foobarflies/pianette/_Resources/Hardware/PCB Files/PDF/BusBoard/BusBoard_etch_silk_bottom.pdf

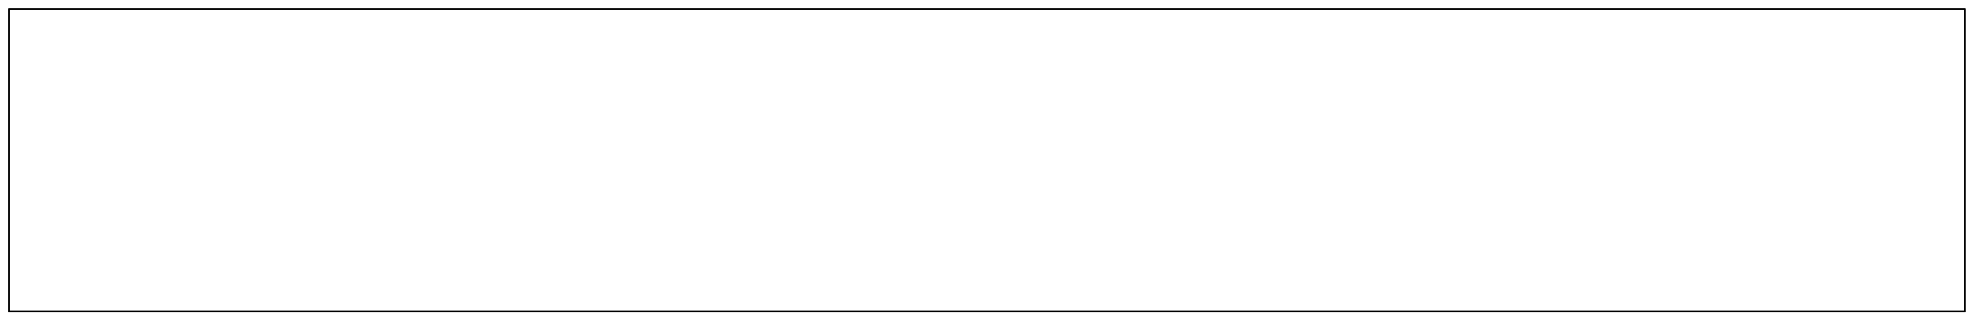
[picture p5: page 1]
