foobarflies/pianette/_Resources/Hardware/PCB Files/PDF/BusBoard/BusBoard_etch_silk_bottom_mirror.pdf

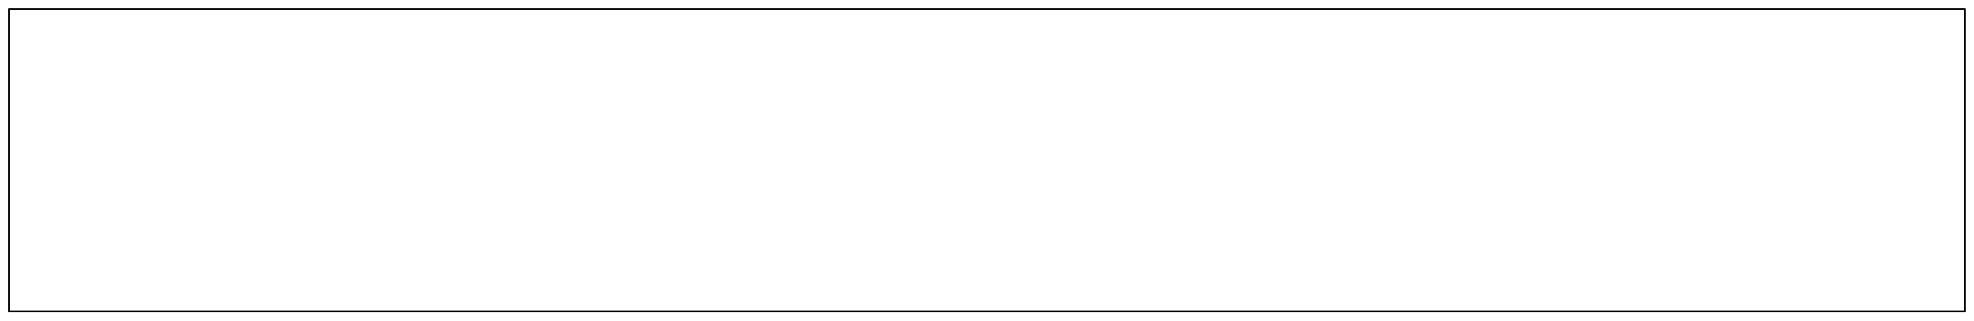
[picture p6: page 1]
