foobarflies/pianette/_Resources/Hardware/PCB Files/PDF/BusBoard/BusBoard_etch_silk_top.pdf

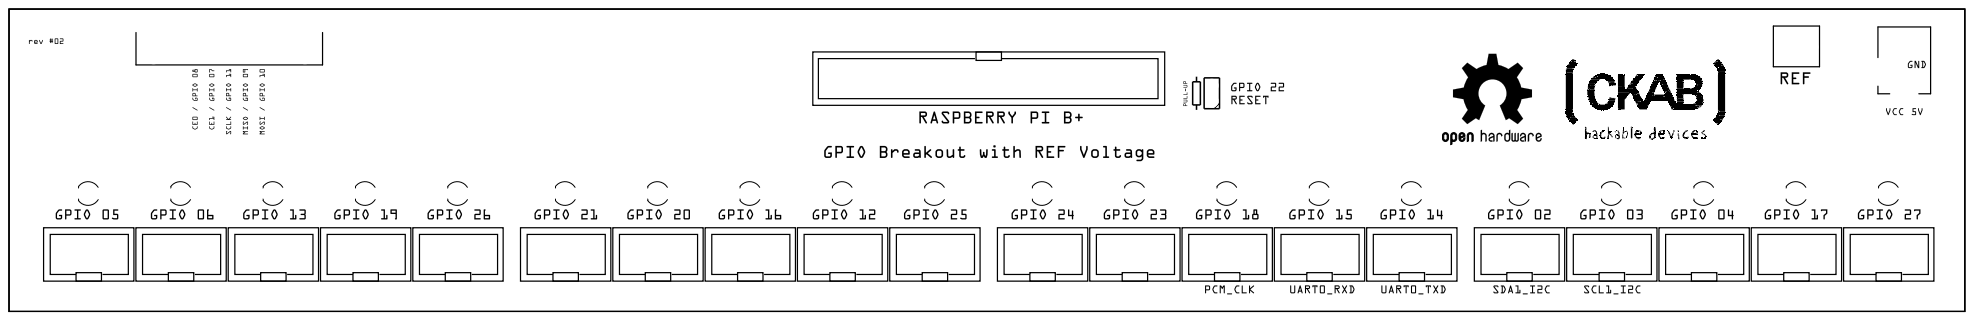
[picture p21: page 1]
