foobarflies/pianette/_Resources/Hardware/PCB Files/PDF/BusBoard/BusBoard_etch_silk_top_mirror.pdf

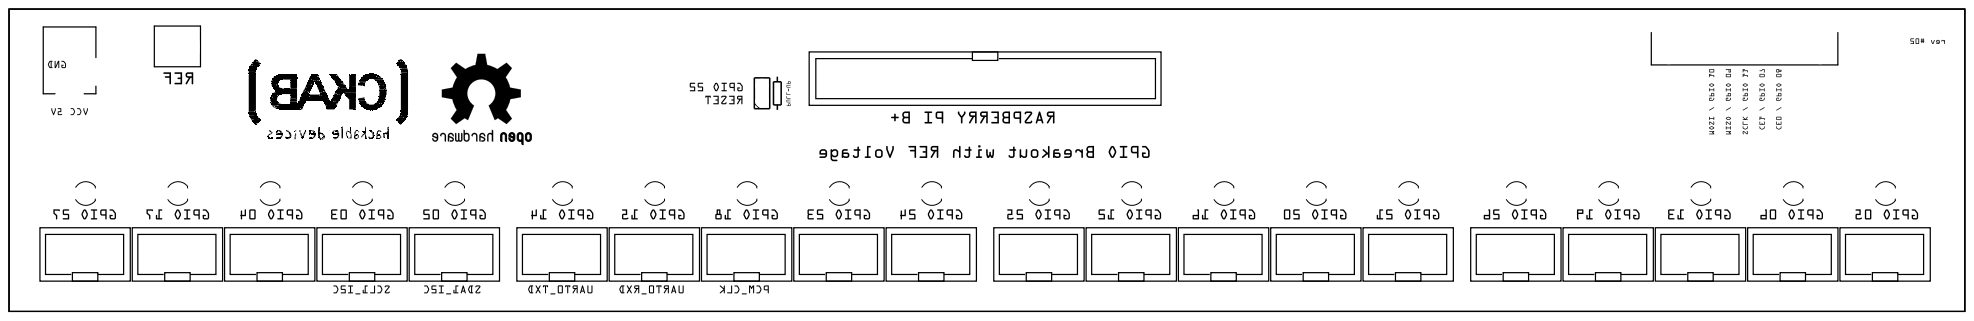
[picture p22: page 1]
