foobarflies/pianette/_Resources/Hardware/PCB Files/PDF/AnalogTrigger/AnalogTrigger_etch_copper_bottom.pdf

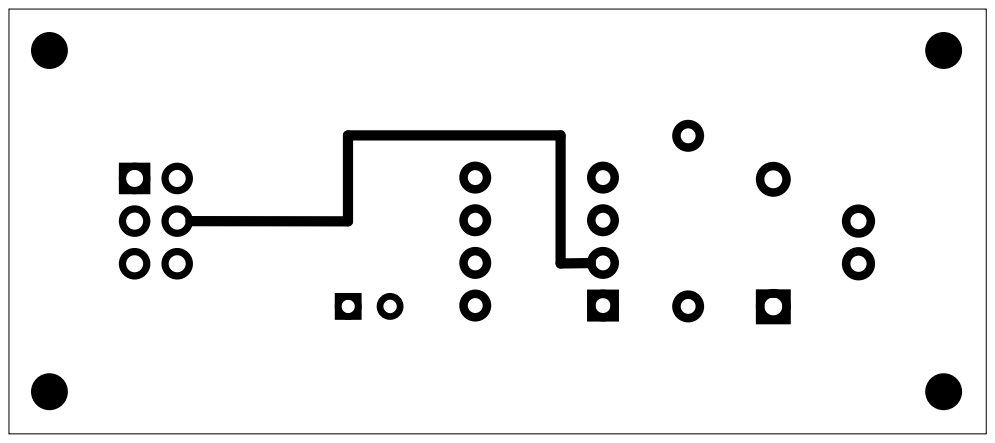
[picture p23: page 1]
