foobarflies/pianette/_Resources/Hardware/PCB Files/PDF/AnalogTrigger/AnalogTrigger_etch_copper_bottom_mirror.pdf

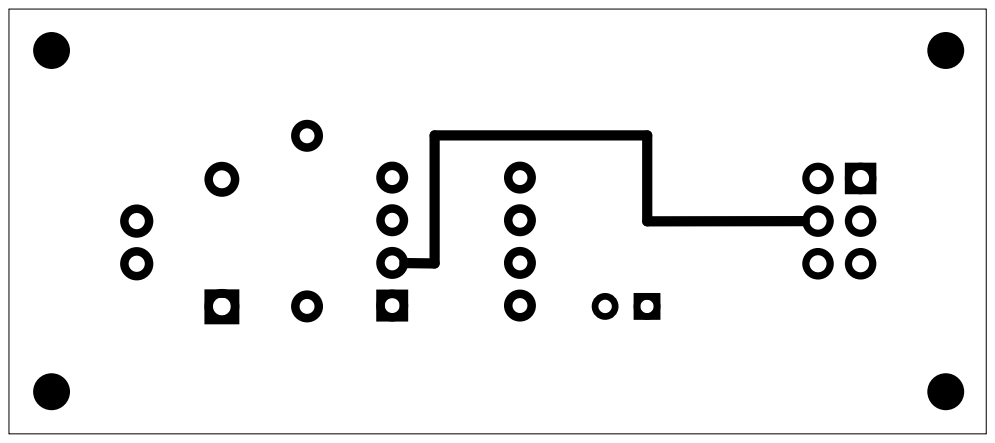
[picture p24: page 1]
