foobarflies/pianette/_Resources/Hardware/PCB Files/PDF/AnalogTrigger/AnalogTrigger_etch_copper_top.pdf

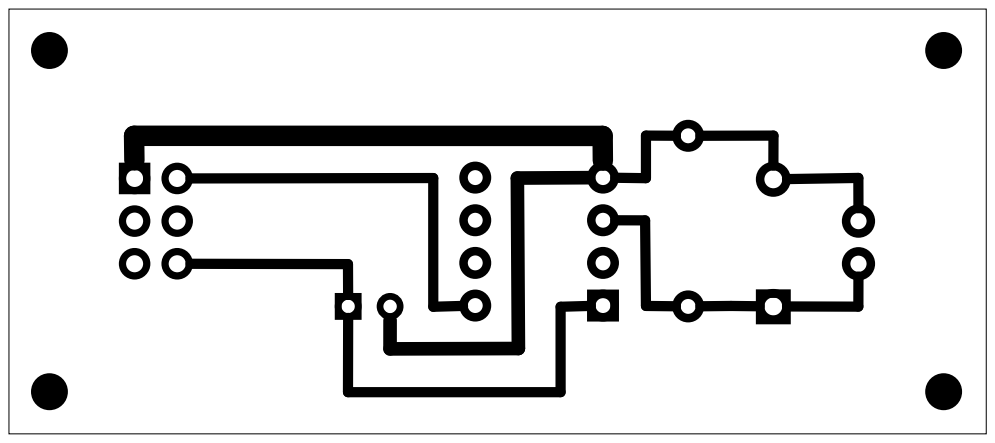
[picture p25: page 1]
