foobarflies/pianette/_Resources/Hardware/PCB Files/PDF/AnalogTrigger/AnalogTrigger_etch_copper_top_mirror.pdf

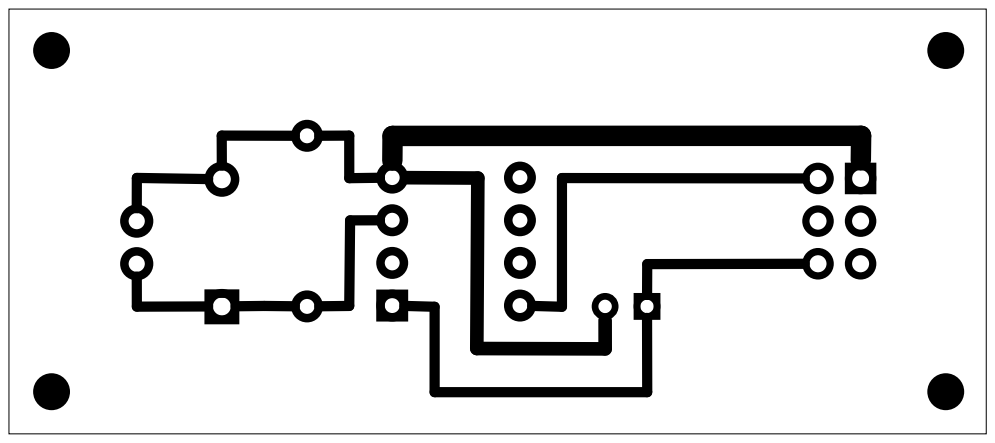
[picture p26: page 1]
