foobarflies/pianette/_Resources/Hardware/PCB Files/PDF/AnalogTrigger/AnalogTrigger_etch_mask_bottom.pdf

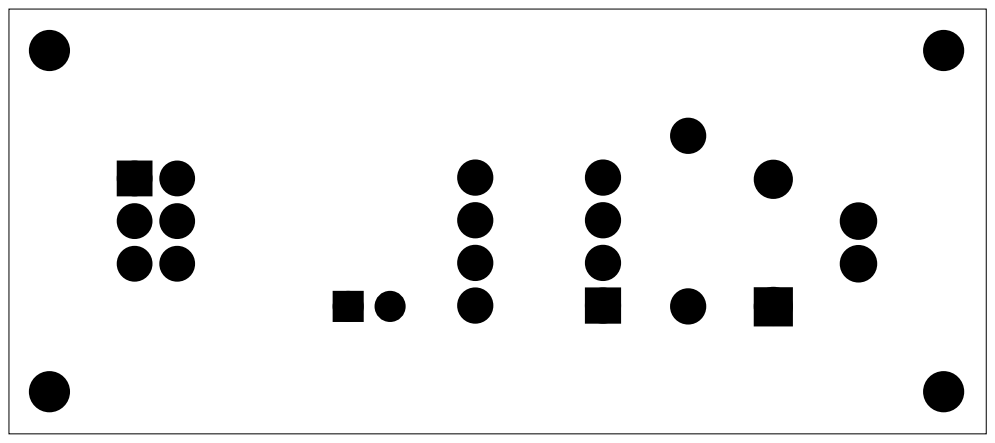
[picture p27: page 1]
