foobarflies/pianette/_Resources/Hardware/PCB Files/PDF/AnalogTrigger/AnalogTrigger_etch_mask_bottom_mirror.pdf

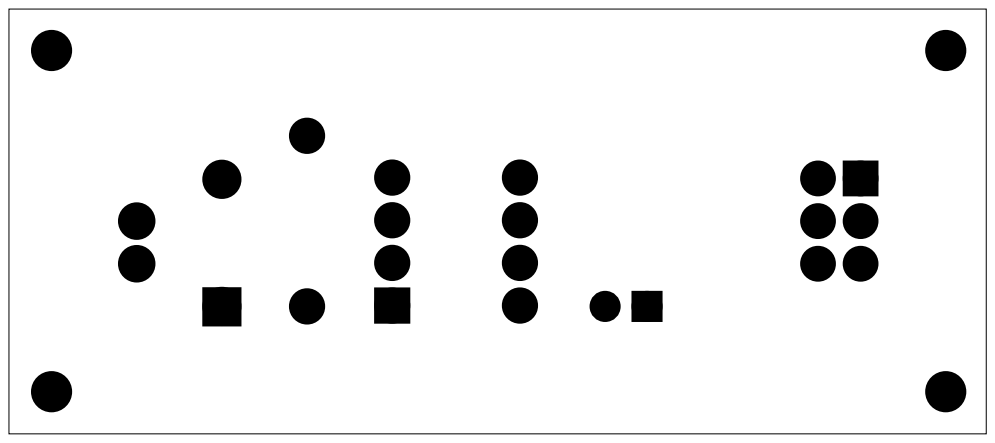
[picture p28: page 1]
