foobarflies/pianette/_Resources/Hardware/PCB Files/PDF/AnalogTrigger/AnalogTrigger_etch_silk_bottom.pdf

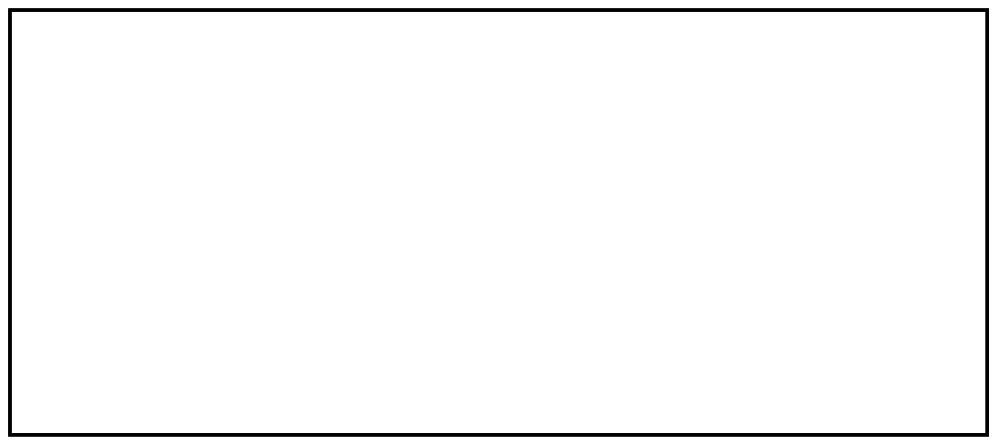
[picture p29: page 1]
