foobarflies/pianette/_Resources/Hardware/PCB Files/PDF/AnalogTrigger/AnalogTrigger_etch_silk_top_mirror.pdf

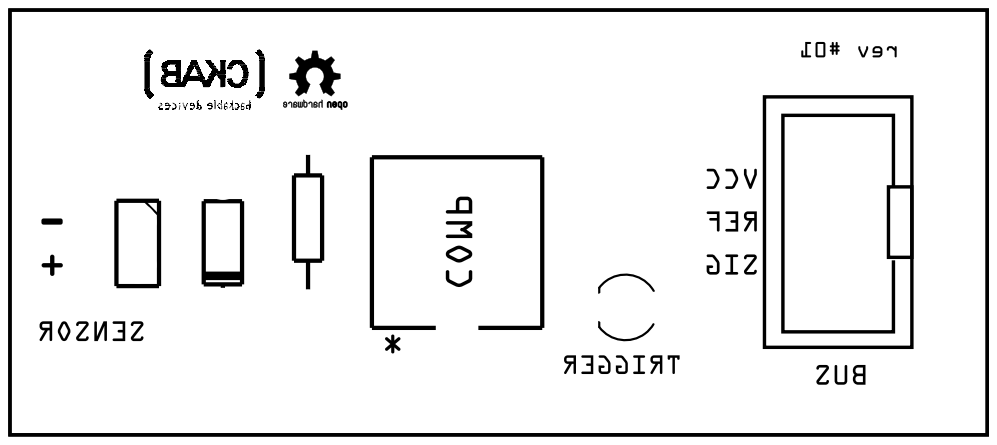
[picture p31: page 1]
