foobarflies/pianette/_Resources/Hardware/PCB Files/PDF/ArduinoBoard/ArduinoBoard_etch_copper_bottom.pdf

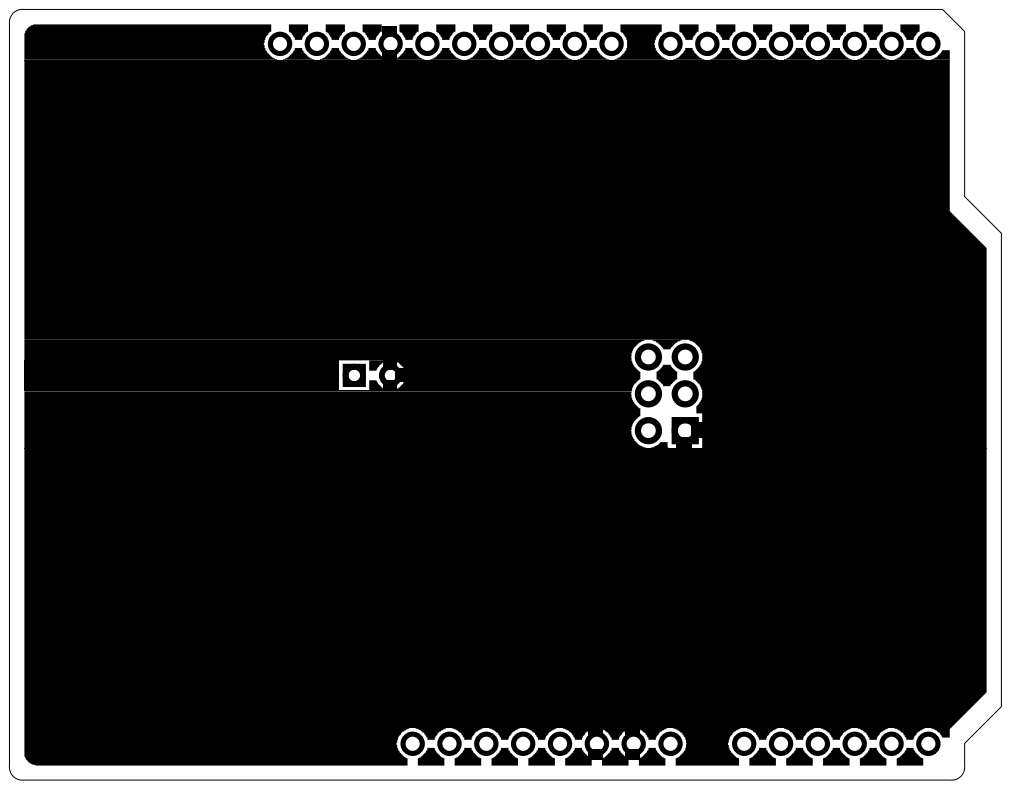
[picture p32: page 1]
