foobarflies/pianette/_Resources/Hardware/PCB Files/PDF/ArduinoBoard/ArduinoBoard_etch_copper_bottom_mirror.pdf

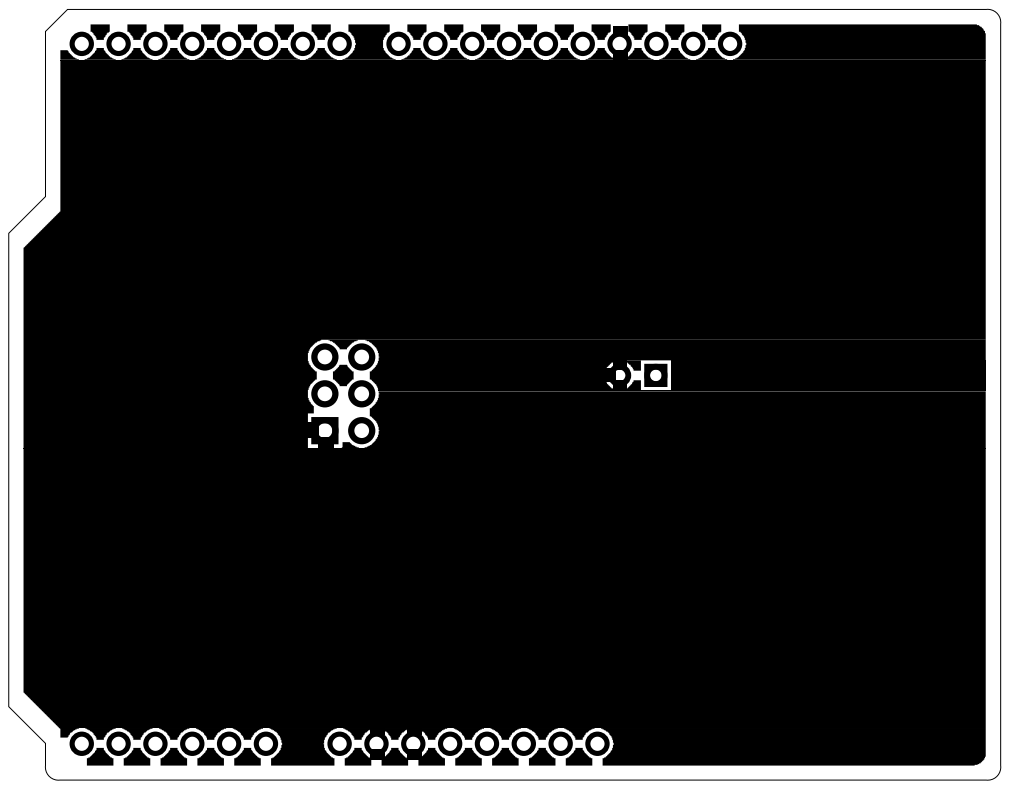
[picture p33: page 1]
