foobarflies/pianette/_Resources/Hardware/PCB Files/PDF/ArduinoBoard/ArduinoBoard_etch_copper_top.pdf

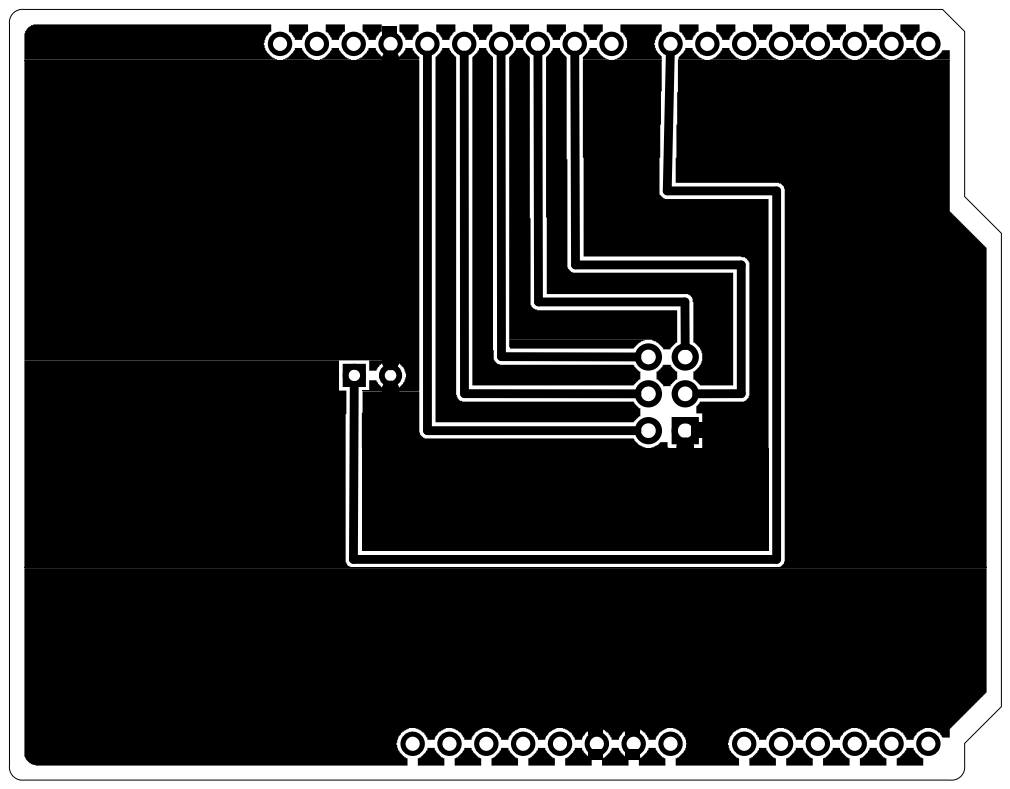
[picture p34: page 1]
