foobarflies/pianette/_Resources/Hardware/PCB Files/PDF/ArduinoBoard/ArduinoBoard_etch_copper_top_mirror.pdf

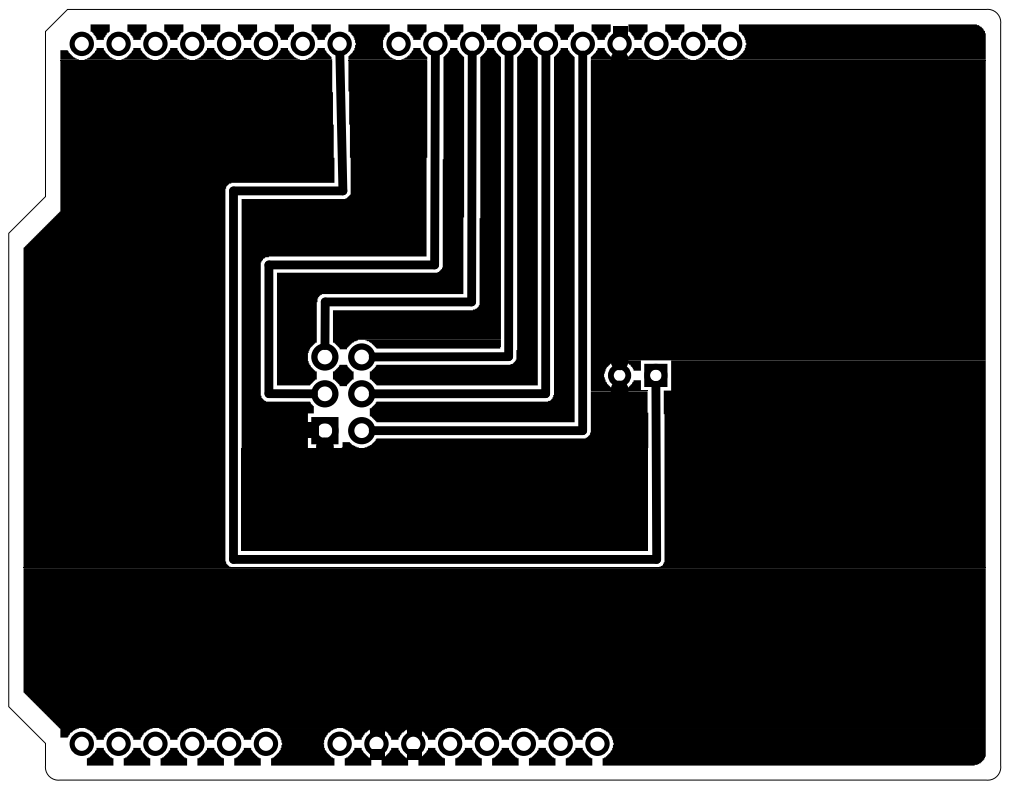
[picture p35: page 1]
