foobarflies/pianette/_Resources/Hardware/PCB Files/PDF/ArduinoBoard/ArduinoBoard_etch_mask_bottom.pdf

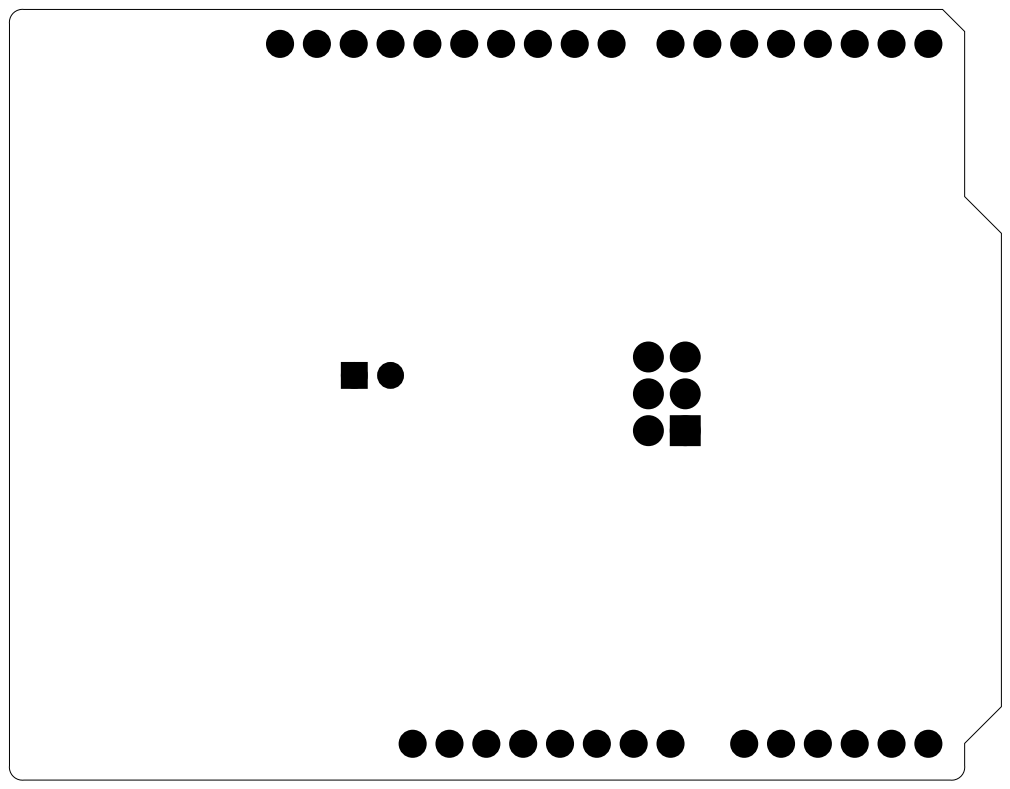
[picture p36: page 1]
