foobarflies/pianette/_Resources/Hardware/PCB Files/PDF/ArduinoBoard/ArduinoBoard_etch_mask_bottom_mirror.pdf

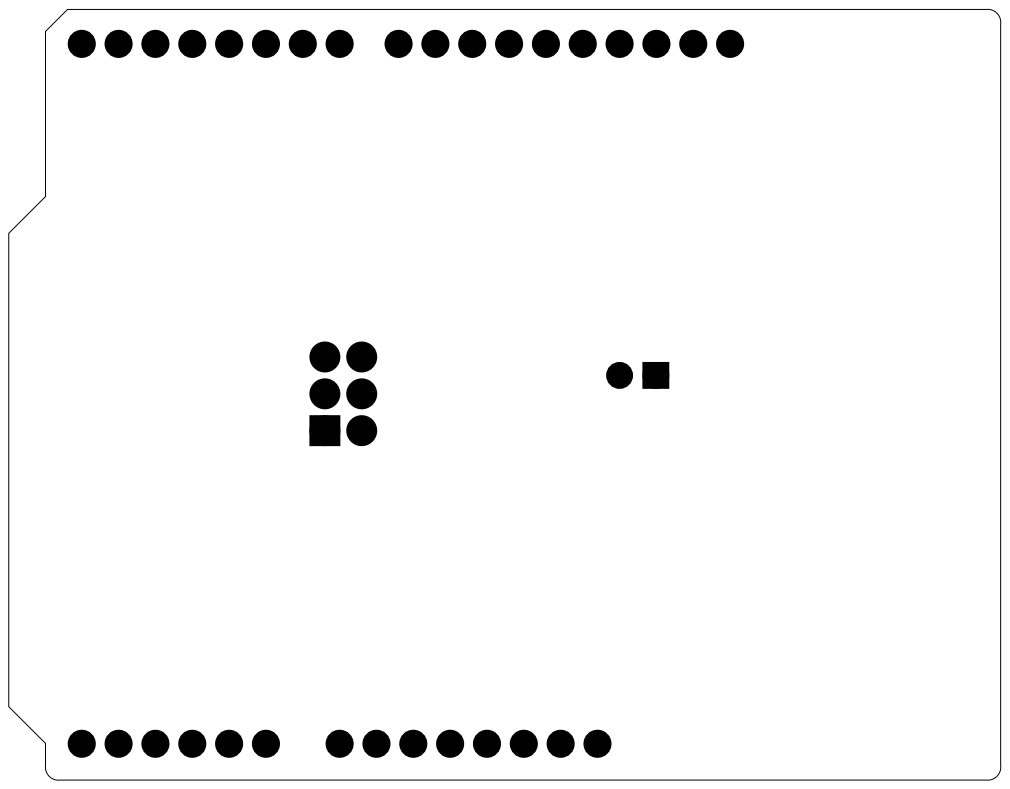
[picture p37: page 1]
