foobarflies/pianette/_Resources/Hardware/PCB Files/PDF/ArduinoBoard/ArduinoBoard_etch_silk_bottom.pdf

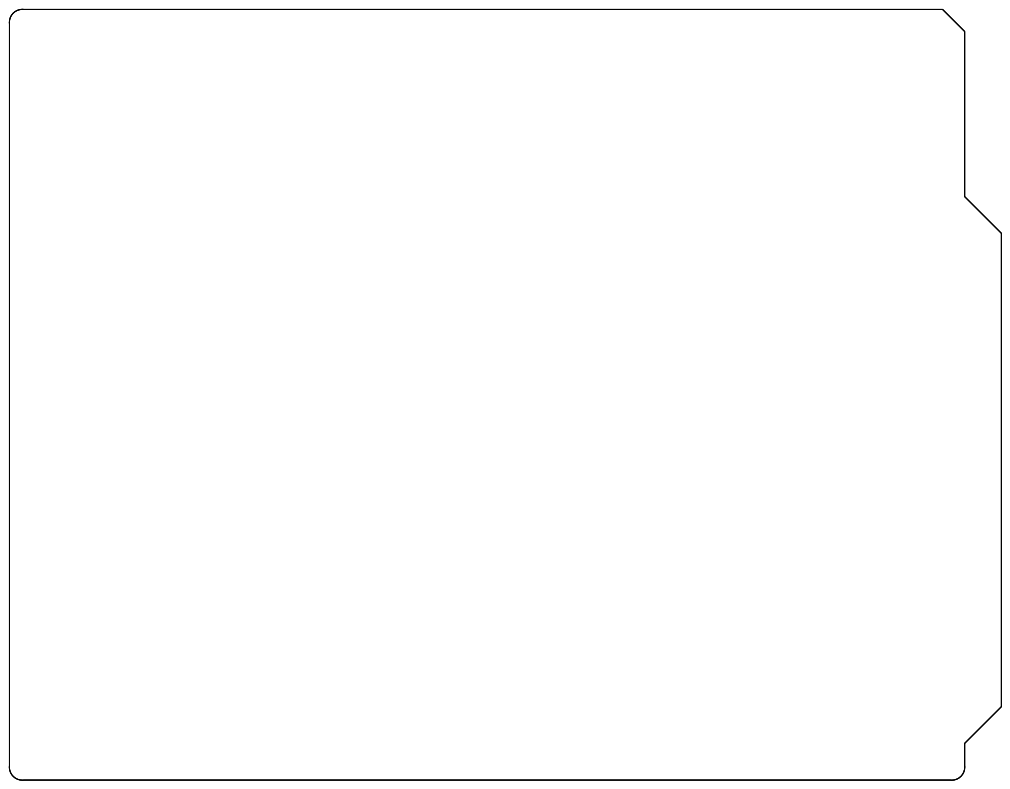
[picture p38: page 1]
