foobarflies/pianette/_Resources/Hardware/PCB Files/PDF/ArduinoBoard/ArduinoBoard_etch_silk_bottom_mirror.pdf

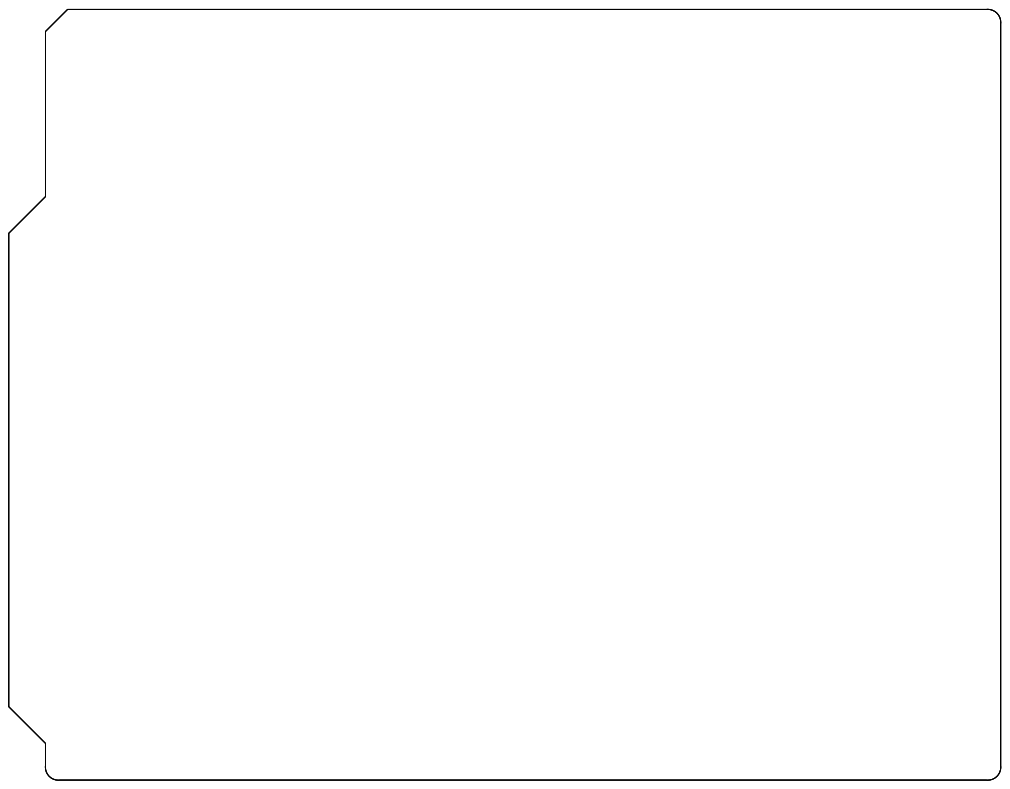
[picture p39: page 1]
