foobarflies/pianette/_Resources/Hardware/PCB Files/PDF/ArduinoBoard/ArduinoBoard_etch_silk_top_mirror.pdf

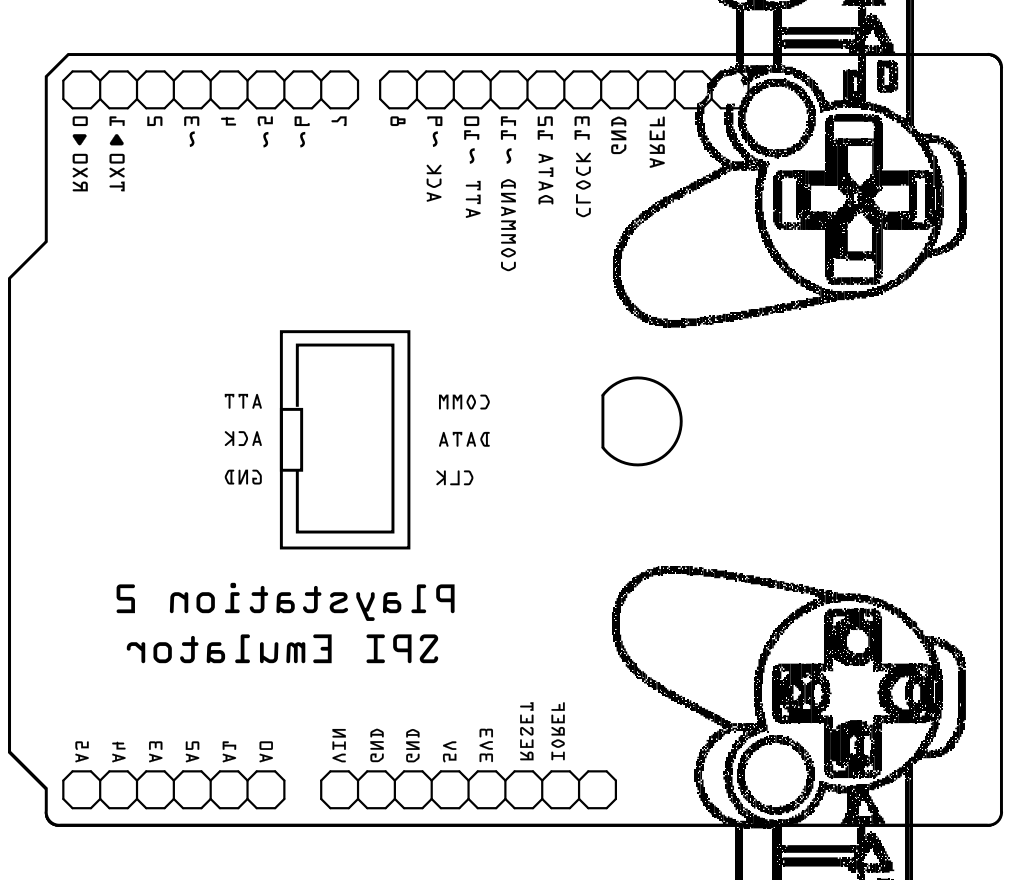
[picture p41: page 1]
