foobarflies/pianette/models/GPIOController.py

# coding=utf-8

from utils import *
import warnings

import RPi.GPIO as GPIO

GPIO.setmode(GPIO.BCM)

# We want to be able to catch warnings, expecially the RuntimeWarning when a pin is already attached
warnings.filterwarnings('error')

# Just to be sure ...
# THIS LINE WILL ISSUE A WARNING THAT CAN HOPEFULLY BE IGNORED
GPIO.cleanup()

"""
# Global GPIO Pin Mapping
"""
GPIO_PIN_ATTACHMENTS = {
    # Bank 1
    5: { "note": "C3" },
    6: { "note": "D3" },
    13: { "note": "E3" },
    19: { "note": "F3" },
    26: { "note": "G3" },

    # Bank 2
    21: { "note": "A4" },
    20: { "note": "B♭4" },
    16: { "note": "B4" },
    12: { "note": "C4" },
    25: None,
    22: { "pull_up_down": GPIO.PUD_UP, "event": GPIO.FALLING, "command": "RESET" },

    # Bank 3
    24: { "note": "C5" },
    23: { "note": "D5" },
    18: { "note": "E♭5" },
    15: { "note": "E5" },
    14: { "note": "F5" },

    # Bank 4
    2: { "note": "G♭5" },
    3: { "note": "G5" },
    4: { "note": "A6" },
    17: { "note": "B♭6" },
    27: { "note": "B6" },
}

class GPIOController:
    def __init__(self, piano_state, controller_state):
        self.piano_state = piano_state
        self.controller_state = controller_state

        # Attach callbacks to pins
        Debug.println("INFO", "Attaching event callbacks to pins ...")

        for pin, attachment in GPIO_PIN_ATTACHMENTS.items():
            if attachment:
                pull_up_down = attachment.get("pull_up_down", GPIO.PUD_DOWN)
                event = attachment.get("event", GPIO.RISING)

                callback = None
                callback_description = None

                if "note" in attachment:
                    callback = self.gpio_pin_note_callback
                    callback_description = "Note %s" % attachment["note"]
                elif "command" in attachment:
                    callback = self.gpio_pin_command_callback
                    callback_description = "Command %s" % attachment["command"]
                if callback is None:
                    Debug.println("FAIL", "Could not attach event callback for pin %2d" % (pin))
                    raise Exception()

                try:
                    GPIO.setup(pin, GPIO.IN, pull_up_down = pull_up_down)
                    GPIO.add_event_detect(pin, event, callback=callback, bouncetime=300)
                except Exception:
                    if (pin in {14, 15, 18}): # UART Pins, we can override
                        Debug.println("WARNING", "UART Pin %2d already in use. Overriding ..." % (pin))
                    else: # Nope nope nope nope, nope.
                        Debug.println("FAIL", "Pin %2d already in use." % (pin))
                        raise
                Debug.println("SUCCESS", "Pin %2d attached to %s" % (pin, callback_description) )
            else:
                Debug.println("WARNING", "Pin %2d not attached" % (pin) )

    def __del__(self):
        # Cleanup GPIOs on object destruction
        GPIO.cleanup()

    # Callback method for PSX Controller Commands
    def gpio_pin_command_callback(self, channel):
        command = GPIO_PIN_ATTACHMENTS[channel]["command"]
        Debug.println("INFO", "Pin %2d activated : triggering PSX Controller Command %s" % (channel, command) )
        self.controller_state.raiseFlag("RESET")

    # Callback method for Piano Notes
    def gpio_pin_note_callback(self,channel):
        note = GPIO_PIN_ATTACHMENTS[channel]["note"]
        Debug.println("INFO", "Pin %2d activated : triggering Piano Note %s" % (channel, note) )
        self.piano_state.raise_note(note)
