foobarflies/pianette/models/Pianette.py

# coding=utf-8

from copy import deepcopy
from utils import *
from models import ConsoleController

import threading

# Pianette Configuration

# Period of I/O cycle, in seconds
PIANETTE_CYCLE_PERIOD = 10/1000 # Seems to properly operate between 7 msecs and 26 msecs (PSX observation)

# Number of cycles before Inputs are processed and sent to Output
PIANETTE_PROCESSING_CYCLES = 2

# Mapping: Piano Notes (input) => PSX Controller Combo (output)
PIANETTE_BUFFERED_STATES_MAPPINGS = [
    # Single Notes (left hand): Moves
    {
        "piano": [ "C3" ],
        "psx_controller": { "LEFT": [ 10 ] },
    },
    {
        "piano": [ "D3" ],
        "psx_controller": { "LEFT": [ 5 ] },
    },
    {
        "piano": [ "F3" ],
        "psx_controller": { "DOWN": [ 10 ] },
    },
    {
        "piano": [ "A4" ],
        "psx_controller": { "RIGHT": [ 5 ] },
    },
    {
        "piano": [ "B4" ],
        "psx_controller": { "RIGHT": [ 10 ] },
    },

    # Single Notes (right hand): Simple Strikes
    {
        "piano": [ "C5" ],
        "psx_controller": { "S": [ 3 ] },
    },
    {
        "piano": [ "D5" ],
        "psx_controller": { "O": [ 3 ] },
    },
    {
        "piano": [ "E5" ],
        "psx_controller": { "X": [ 3 ] },
    },
    {
        "piano": [ "F5" ],
        "psx_controller": { "S": [ 3 ] },
    },
    {
        "piano": [ "G5" ],
        "psx_controller": { "O": [ 3 ] },
    },
    {
        "piano": [ "A6" ],
        "psx_controller": { "T": [ 3 ] },
    },
    {
        "piano": [ "B6" ],
        "psx_controller": { "T": [ 3 ] },
    },

    # Chords (left hand): Combo Moves!
    {
        # LEFT1 + CL1 + CL2 (Do majeur) => UP
        "piano": [ "C3", "E3", "G3" ],
        "psx_controller": { "UP" : [ 3 ] },
    },
    {
        # LEFT1 + CL4 (Do octave) => UP
        "piano": [ "C3", "C4" ],
        "psx_controller": { "UP" : [ 3 ] },
    },
    {
        # LEFT1 + CL1 + CL2 + CL3 (Do majeur 7e) => UP + Kick droit (ou gauche suivant player)
        "piano": [ "C3", "E3", "G3", "B♭4" ],
        "psx_controller": { "UP" : [ 3 ], "X": [ -1, 3 ] },
    },
    {
        # CL1 + CL2 + CL4 (Do Majeur premier renversement) => UP+RIGHT
        "piano": [ "E3", "G3", "C4" ],
        "psx_controller": { "RIGHT" : [ 3 ], "UP": [ -1, 3 ] },
    },
    {
        # LEFT1 + DOWN (Do Dim 4) => DOWN+LEFT
        "piano": [ "C3", "F3" ],
        "psx_controller": { "DOWN" : [ 3 ], "LEFT": [ 3 ] },
    },
    {
        # LEFT2 + DOWN (Ré Min) => DOWN+LEFT
        "piano": [ "D3", "F3" ],
        "psx_controller": { "DOWN" : [ 3 ], "LEFT": [ 3 ] },
    },
    {
        # RIGHT1 + DOWN (Ré min) => RIGHT+DOWN
        "piano": [ "A4", "F3" ],
        "psx_controller": { "DOWN" : [ 3 ], "RIGHT": [ 3 ] },
    },
    {
        # RIGHT2 + DOWN (Si) => RIGHT+DOWN
        "piano": [ "B4", "F3" ],
        "psx_controller": { "DOWN" : [ 3 ], "RIGHT": [ 3 ] },
    },

    # Chords (right hand): Combo Strikes!

    {
        # S1 + X1 + O1 (Do majeur) => Tatsukami
        "piano": [ "C5", "E5", "D5" ],
        "psx_controller": { "DOWN" : [ 1, 3 ],  "RIGHT" : [ -1, 3, 3 ], "X" : [ -1, -3, -3, 10] },
    },
    {
        # S1 + X1 + O1 + CR3 (Do 7e) => Hadouken
        "piano": [ "C5", "E5", "D5", "B♭6" ],
        "psx_controller": { "DOWN" : [ 1, 3 ],  "LEFT" : [ -1, 3, 3 ], "S" : [ -1, -3, -3, 10] },
    },
    {
        # S1 + S2 + T1 (Do 6) => ?
        "piano": [ "C5", "F5", "A6" ],
        "psx_controller": {},
    },
    {
        # S1 + CR1 + O1 (Do min) => ?
        "piano": [ "C5", "E♭5", "D5" ],
        "psx_controller": {},
    },
    {
        # S1 + CR1 + O1 + CR3 (Do min 7e) => ?
        "piano": [ "C5", "E♭5", "D5", "B♭6" ],
        "psx_controller": {},
    },
    {
        # S1 + CR1 + CR2 + CR3 (Dim 3) => ?
        "piano": [ "C5", "E5", "G♭5", "B♭6" ],
        "psx_controller": {},
    },

    # "Combo Enabler" keys, no direct mapping
    # "E3" (AKA "CL1")
    # "G3" (AKA "CL2")
    # "B♭4" (AKA "CL3")
    # "C4" (AKA "CL4")
    # "E♭5" (AKA "CR1")
    # "G♭5" (AKA "CR2")
    # "B♭6" (AKA "CR3")
]

# Assign a unique, combinable bitid to configured notes
_NOTE_BITIDS = {}

_current_note_bitid = 0b1
for buffered_state_mapping in PIANETTE_BUFFERED_STATES_MAPPINGS:
    for note in buffered_state_mapping["piano"]:
        if not note in _NOTE_BITIDS:
            _NOTE_BITIDS[note] = _current_note_bitid
            _current_note_bitid <<= 1
del _current_note_bitid

# Structure Buffered States Mapping using Piano "Chords" bitids (combination of Note bitids)
# Rank chords as follows:
#   1- chords with more notes have a higher priority
#   2- for an equal number of notes, chords declared first in config have a higher priority
_ranked_chord_bitids_for_note_count = {}

_BUFFERED_STATES_MAPPING_FOR_CHORD_BITID = {}
for buffered_state_mapping in PIANETTE_BUFFERED_STATES_MAPPINGS:
    chord_bitid = 0b0
    note_count = len(buffered_state_mapping["piano"])

    for note in buffered_state_mapping["piano"]:
        chord_bitid |= _NOTE_BITIDS[note]

    _BUFFERED_STATES_MAPPING_FOR_CHORD_BITID[chord_bitid] = buffered_state_mapping
    chord_bitids = _ranked_chord_bitids_for_note_count.get(note_count, [])
    chord_bitids.append(chord_bitid)
    _ranked_chord_bitids_for_note_count[note_count] = chord_bitids

_RANKED_CHORD_BITIDS = []
for note_count in sorted(list(_ranked_chord_bitids_for_note_count.keys()), reverse = True):
    _RANKED_CHORD_BITIDS.extend(_ranked_chord_bitids_for_note_count[note_count])
del _ranked_chord_bitids_for_note_count

def get_notes_chord_bitid(notes):
    notes_bitids = [ _NOTE_BITIDS[note] for note in notes ]
    notes_chord_bitid = 0b0
    for bitid in notes_bitids:
        notes_chord_bitid |= bitid
    return notes_chord_bitid

def get_ranked_chord_bitids_including_at_least_one_of_notes(notes, from_chord_bitids_pool = _RANKED_CHORD_BITIDS):
    notes_chord_bitid = get_notes_chord_bitid(notes)

    ranked_notes_chord_bitids = []
    for chord_bitid in from_chord_bitids_pool:
        if (chord_bitid & notes_chord_bitid):
            ranked_notes_chord_bitids.append(chord_bitid)

    return ranked_notes_chord_bitids

class Pianette(object):
    def __init__(self, piano_state, psx_controller_state):
        self.piano_state = piano_state
        self.psx_controller_state = psx_controller_state

        # Instantiate the console controller that is responsible for sendint out the psx constroller state to the console
        self.console_controller = ConsoleController(self.psx_controller_state)

        # Upcoming state cycles for the Piano Notes (input)
        self.piano_buffered_states = {
            "C3": [],
            "D3": [],
            "E3": [],
            "F3": [],
            "G3": [],
            "A4": [],
            "B♭4": [],
            "B4": [],
            "C4": [],
            "C5": [],
            "D5": [],
            "E♭5": [],
            "E5": [],
            "F5": [],
            "G♭5": [],
            "G5": [],
            "A6": [],
            "B♭6": [],
            "B6": [],
        }

        # Upcoming state cycles for the PSX Controller (output)
        self.psx_controller_buffered_states = {
            "T" : [],
            "S" : [],
            "X" : [],
            "O" : [],
            "UP" : [],
            "DOWN" : [],
            "LEFT" : [],
            "RIGHT" : [],
            "SELECT" : [],
            "START" : [],
        }

        self._timer = None
        self._timer_interval = PIANETTE_CYCLE_PERIOD
        self._timer_is_running = False

        # Start the timer thread that will cycle buffered states at each interval
        self.start_timer()
        Debug.println("INFO", "Pianette buffered states timer thread started at %f secs interval" % self._timer_interval)

    def __del__(self):
        if hasattr(self, '_timer'):
            self.stop_timer()

    def _run_timer(self):
        self._timer_is_running = False
        self.start_timer()
        self.cycle_buffered_states()

    def start_timer(self):
        if not self._timer_is_running:
            self._timer = threading.Timer(self._timer_interval, self._run_timer)
            self._timer.start()
            self.is_running = True

    def stop_timer(self):
        self._timer.cancel()
        self._timer_is_running = False

    def cycle_buffered_states(self):
        # Input Piano Notes to Piano Buffered States
        for piano_note in self.piano_state.get_notes_keys():
            if self.piano_state.is_note_raised(piano_note):
                Debug.println("INFO", "Processing Piano Note %s" % (piano_note))
                self.piano_buffered_states[piano_note].append({ "cycles_remaining": PIANETTE_PROCESSING_CYCLES })
                self.piano_state.clear_note(piano_note)

        # Process Buffered States: Determine piano note or chord
        # Notes that have reached their last cycle "lead" the chord determination
        # Other notes may be used to "complement" lead notes.
        # If a winning chord is found, push corresponding combo to PSX Controller buffer
        # If complementary notes are actually used, they are discarded from buffer.
        lead_notes = []
        complementary_notes = []
        for piano_note in self.piano_buffered_states.keys():
            processed_buffered_states = []
            for buffered_state in self.piano_buffered_states[piano_note]:
                if buffered_state["cycles_remaining"] == 0:
                    lead_notes.append(piano_note)
                else:
                    complementary_notes.append(piano_note)
                    buffered_state["cycles_remaining"] -= 1
                    processed_buffered_states.append(buffered_state)
            self.piano_buffered_states[piano_note] = processed_buffered_states

        if lead_notes:
            Debug.println("INFO", "Processing Piano Notes: lead=%s, complementary=%s" % (lead_notes, complementary_notes))
            ranked_chord_bitids = get_ranked_chord_bitids_including_at_least_one_of_notes(lead_notes)

            all_notes_chord_bitid = get_notes_chord_bitid(lead_notes + complementary_notes)
            ranked_winning_chord_bitids = [chord_bitid for chord_bitid in ranked_chord_bitids if not ((all_notes_chord_bitid & chord_bitid) ^ chord_bitid)]

            if ranked_winning_chord_bitids:
                winning_chord_bitid = ranked_winning_chord_bitids[0]
                winning_states_mapping = deepcopy(_BUFFERED_STATES_MAPPING_FOR_CHORD_BITID[winning_chord_bitid])

                # Push piano command to PSX Controller buffer, clearing any pending combo
                for control in self.psx_controller_buffered_states.keys():
                    self.psx_controller_buffered_states[control] = winning_states_mapping["psx_controller"].get(control, [])

                # Clear winning chord notes from the piano buffer
                for piano_note in self.piano_buffered_states.keys():
                    if _NOTE_BITIDS[piano_note] & winning_chord_bitid:
                        if self.piano_buffered_states[piano_note]:
                            self.piano_buffered_states[piano_note] = self.piano_buffered_states[piano_note][1:]

        # Output PSX Controller Buffered states to PSX Controller
        for psx_control, buffered_state in self.psx_controller_buffered_states.items():
            if buffered_state:
                cyclesCount = buffered_state.pop(0)
                if cyclesCount > 0:
                    Debug.println("INFO", "Triggering PSX Control %s" % psx_control)
                    self.psx_controller_state.raiseFlag(psx_control)
                    cyclesCount-= 1
                    buffered_state.insert(0, cyclesCount)
                elif cyclesCount < 0:
                    Debug.println("INFO", "Keeping PSX Control %s Clear" % psx_control)
                    self.psx_controller_state.clearFlag(psx_control)
                    cyclesCount+= 1
                    buffered_state.insert(0, cyclesCount)
                else:
                    Debug.println("INFO", "Clearing PSX Control %s" % psx_control)
                    Debug
                    self.psx_controller_state.clearFlag(psx_control)

        self.console_controller.sendStateBytes()
